gratinDeTopinambour/LCD_CLOCK/Program/Drivers/LCD_4DIGIT/Inc/7segment_font.h

/*
 * 7segment_font.h
 *
 *  Created on: 31 juil. 2026
 *      Author: valentin
 */

#ifndef LCD_4DIGIT_INC_7SEGMENT_FONT_H_
#define LCD_4DIGIT_INC_7SEGMENT_FONT_H_

#include <stdint.h>

extern const uint8_t font7seg[];

#endif /* LCD_4DIGIT_INC_7SEGMENT_FONT_H_ */
