gratinDeTopinambour/LCD_CLOCK/Program/Drivers/LCD_4DIGIT/Src/7segment_font.c

/*
 * 7segment_font.c
 *
 *  Created on: 31 juil. 2026
 *      Author: valentin
 */

#include "../../LCD_4DIGIT/Inc/7segment_font.h"

const uint8_t font7seg [] =
{
		//segment
		//  -A-
		// |   |
		// F   B
		// |   |
		//  -G-
		// |   |
		// E   C
		// |   |
		//  -D-
		//ABCDEFG.
		0b00000000, //' '

		0b11111100, //0
		0b01100000, //1
		0b11011010, //2
		0b11110010, //3
		0b01100110, //4
		0b10110110, //5
		0b10111110, //6
		0b11100000, //7
		0b11111110, //8
		0b11110110, //9

		0b11101110, //A
		0b00111110, //B
		0b10011100, //C
		0b01111010, //D
		0b10011110, //E
		0b10001110, //F
		0b10111100, //G
		0b00101110, //H
		0b01100000, //I
		0b01111000, //J
		0b10101110, //K
		0b00011100, //L
		0b10101000, //M
		0b00101010, //N
		0b00111010, //O
		0b11001110, //P
		0b11100110, //Q
		0b00001010, //R
		0b10110110, //S
		0b00011110, //T
		0b01111100, //U
		0b00111000, //V
		0b01010100, //W
		0b01101110, //X
		0b01110110, //Y
		0b11011010, //Z

		0b11000110, //*


};
